MOSH-Insa-Toulouse/TAOUFIKI_DESOUBEAUX/KiCad/Composants/OLED/Empreinte OLED.png

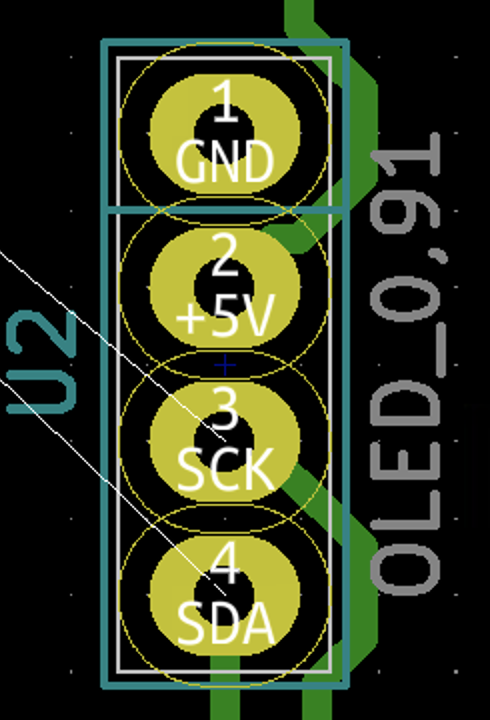
KiCad/Composants/OLED/Empreinte OLED.png
